fharold/rpi2040-lcd-gauge/img/bg_gauge_oil_p.png

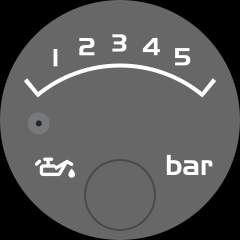
img/bg_gauge_oil_p.png
