fharold/rpi2040-lcd-gauge/img/bg_gauge_oil_t_dark.png

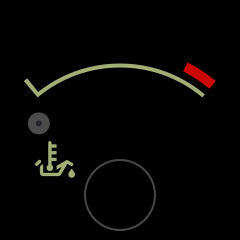
img/bg_gauge_oil_t_dark.png
